ABalanuta/motor-on-roller-blind-ws/NidayandHelper.h

#ifndef NidayandHelper_h
#define NidayandHelper_h

#include "Arduino.h"
#include "FS.h"
#include <ArduinoJson.h>
#include <PubSubClient.h>
#include <WiFiClient.h>
#include <WiFiManager.h>
#include <list>

class NidayandHelper {
  public:
    NidayandHelper();
    boolean loadconfig();
    JsonVariant getconfig();
    boolean saveconfig(JsonVariant json);

    String mqtt_gettopic(String type, String dev_name);

    void mqtt_reconnect(PubSubClient& psclient);
    void mqtt_reconnect(PubSubClient& psclient, std::list<const char*> topics);
    void mqtt_reconnect(PubSubClient& psclient, String uid, String pwd);
    void mqtt_reconnect(PubSubClient& psclient, String uid, String pwd, std::list<const char*> topics);

    void mqtt_publish(PubSubClient& psclient, String topic, String payload);

    void resetsettings(WiFiManager& wifim);

  private:
    JsonVariant _config;
    String _configfile;
    String _mqttclientid;
};

#endif
